DuncanB6/dashlight-hardware/media/IMG_6152.jpg

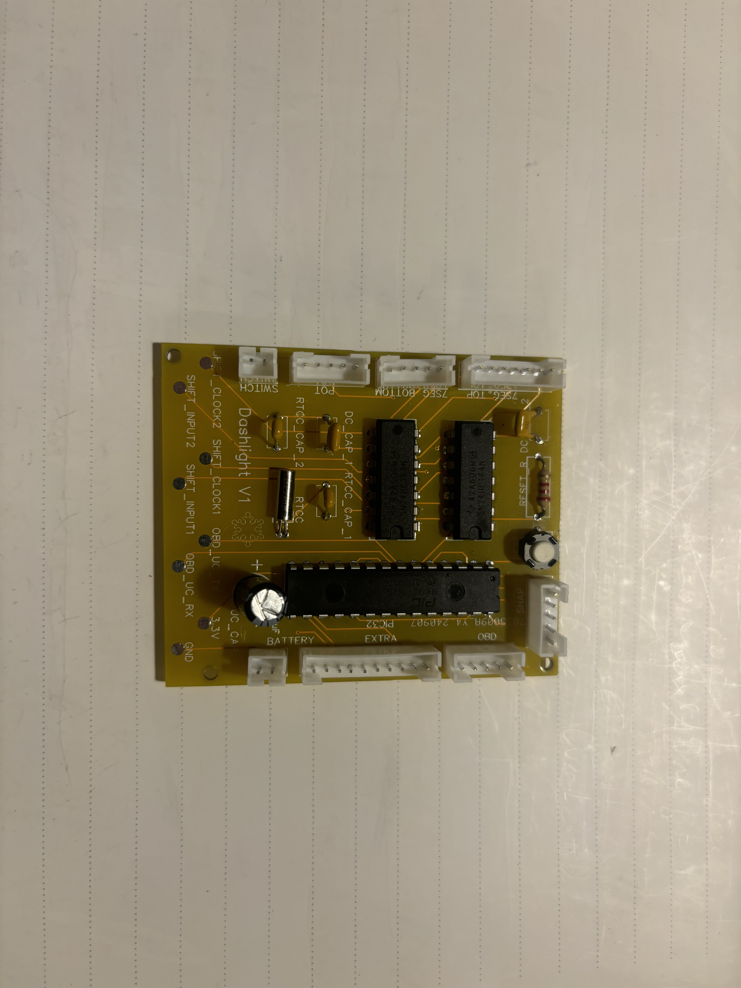
media/IMG_6152.jpg
